4ilo/knx-temperature-monitor/Temperature_monitor_1.1/module/Inc/MAX31865.h

/**
 * Olivier Van den Eede (4ilo) 2019
 * This library uses the MAX31865 RTD-to-Digital Converter to measure the temperature using a Pt100 or Pt1000 temperature probe.
 *
 * This library is written for Stm32f4 microcontrollers using the stm32-HAL software library.
 * The usage of software SPI in this library is due to issues with reading data using the SPI-HAL functions.
 */
#ifndef MAX31865_LIB_MAX31865_H
#define MAX31865_LIB_MAX31865_H

#include "stm32f0xx_hal.h"
#include "cmsis_os.h"

/********************* MAX31865 registers and config bits *********************/
#define MAX31865_READ                   0x00
#define MAX31865_WRITE                  0x80
#define MAX31856_RTDMSB_REG             0x01
#define MAX31856_CONFIG_REG             0x00
#define MAX31856_CONFIG_BIAS            0x80
#define MAX31856_CONFIG_1SHOT           0x20
#define MAX31856_CONFIG_3WIRE           0x10
#define MAX31856_CONFIG_MODEAUTO        0x40


/********************* Constants *********************/
#define RREF 430                        // Reference resistor
#define FACTOR 32768                    // 2^15 used for data to resistance conversion
#define ALPHA 0.003851                  // PT-100 temperature coefficient
#define MAX_AVERAGE 10

/********************* General defines *********************/
#define ON 1
#define OFF 0
#define DELAY(x) osDelay(x)


/********************* MAX31865_GPIO pinout struct *********************/
typedef struct {
    GPIO_TypeDef *CE_PORT;
    uint16_t CE_PIN;

    GPIO_TypeDef *CLK_PORT;
    uint16_t CLK_PIN;

    GPIO_TypeDef *MOSI_PORT;
    uint16_t MOSI_PIN;

    GPIO_TypeDef *MISO_PORT;
    uint16_t MISO_PIN;

    float moving_average;
    float value;
    uint8_t counter;
} MAX31865_GPIO;


/********************* Public functions *********************/
float MAX31865_readTemp(MAX31865_GPIO* gpio);
void MAX31865_init(MAX31865_GPIO *max_gpio, uint8_t wires);

#endif //MAX31865_LIB_MAX31865_H
